YagoTudela/Galaksija_Plus/PS2_Adapter/GalaksijaPS2_v10_RetroBertie.jpg

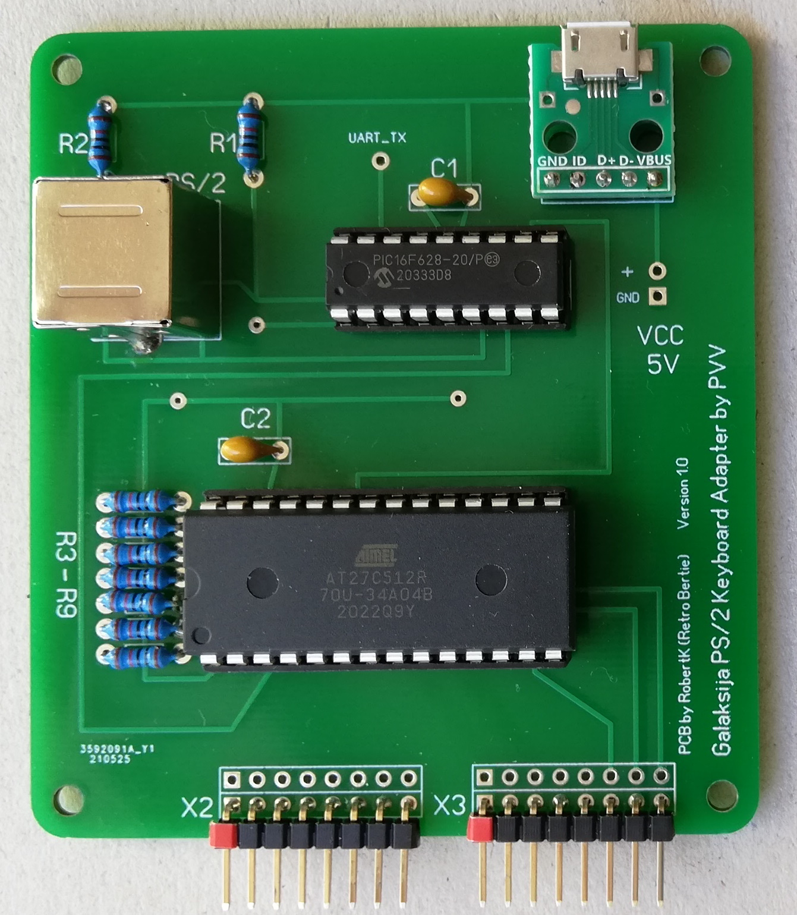
PS2_Adapter/GalaksijaPS2_v10_RetroBertie.jpg
