YagoTudela/Galaksija_Plus/SoundGenerator/SoundGeneratorPVV_01.png

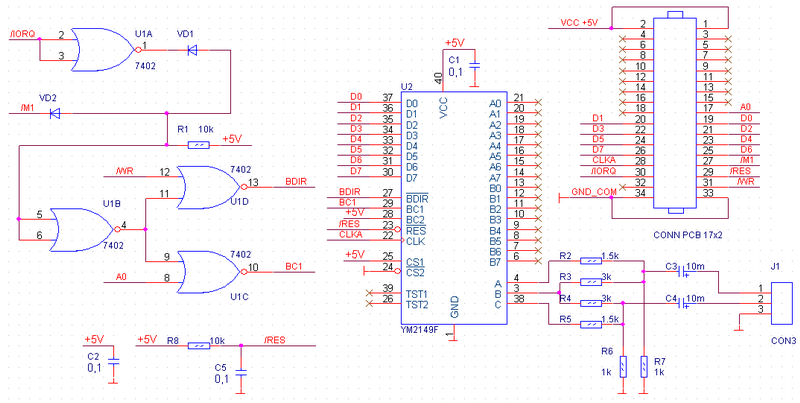
SoundGenerator/SoundGeneratorPVV_01.png
