YagoTudela/Galaksija_Plus/SoundGenerator/SoundGeneratorPVV_02.png

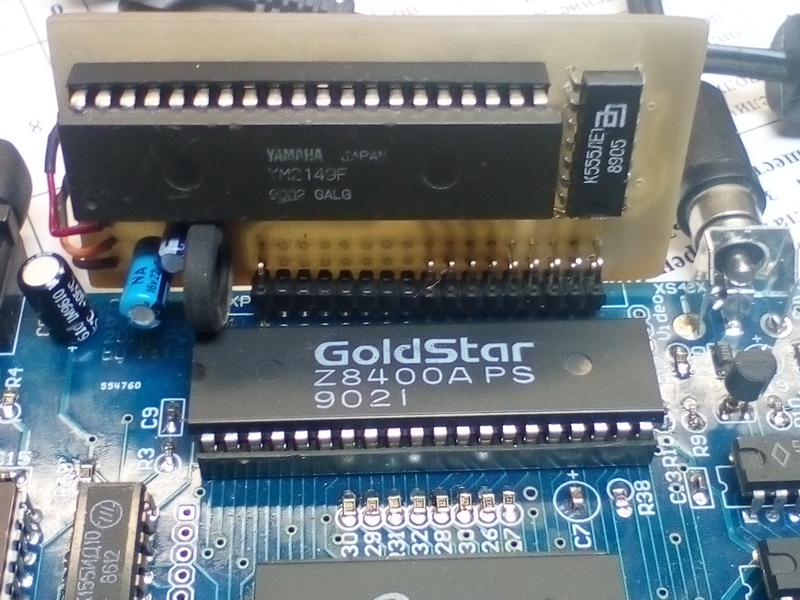
SoundGenerator/SoundGeneratorPVV_02.png
